sparkfun/SparkFun_Buck_Regulator_AP63357DV-7/docs/img/hookup_guide/assembly-jumper_enable_pin.gif

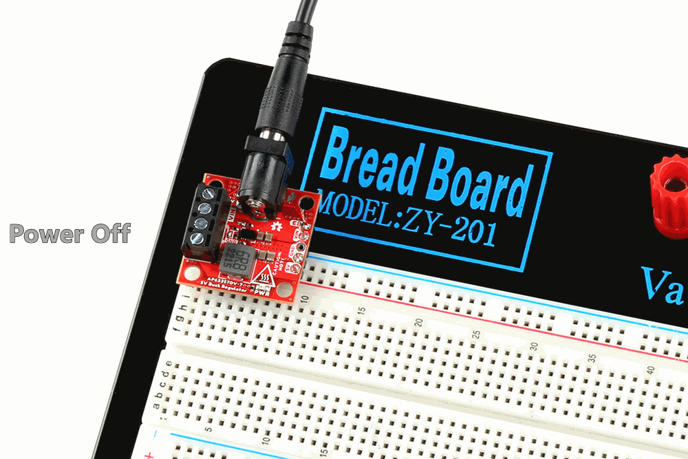
docs/img/hookup_guide/assembly-jumper_enable_pin.gif
