sparkfun/SparkFun_Buck_Regulator_AP63357DV-7/docs/img/hookup_guide/baby-bottom.jpg

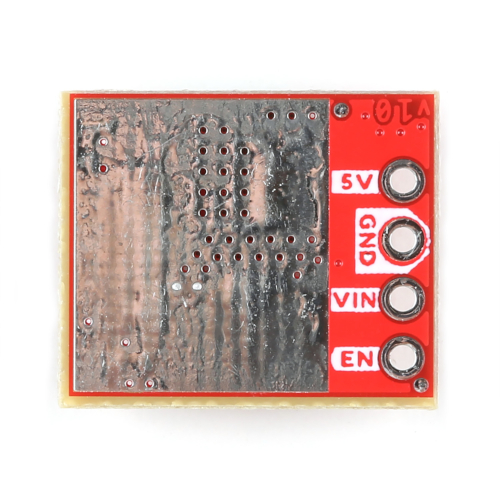
docs/img/hookup_guide/baby-bottom.jpg
