sparkfun/SparkFun_Buck_Regulator_AP63357DV-7/docs/img/hookup_guide/buck-power_connections.jpg

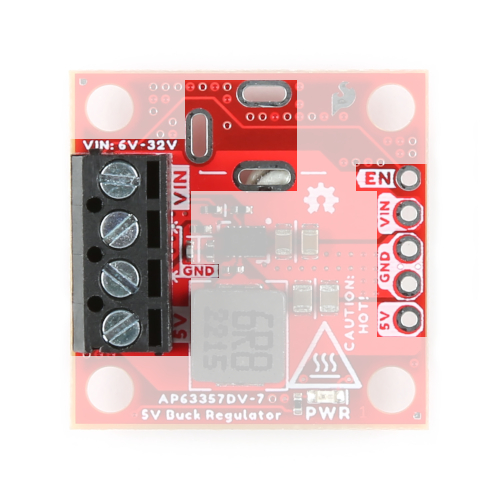
docs/img/hookup_guide/buck-power_connections.jpg
